lmtreser/Arduino-VGA-Games/case/images/buttoncap110.png

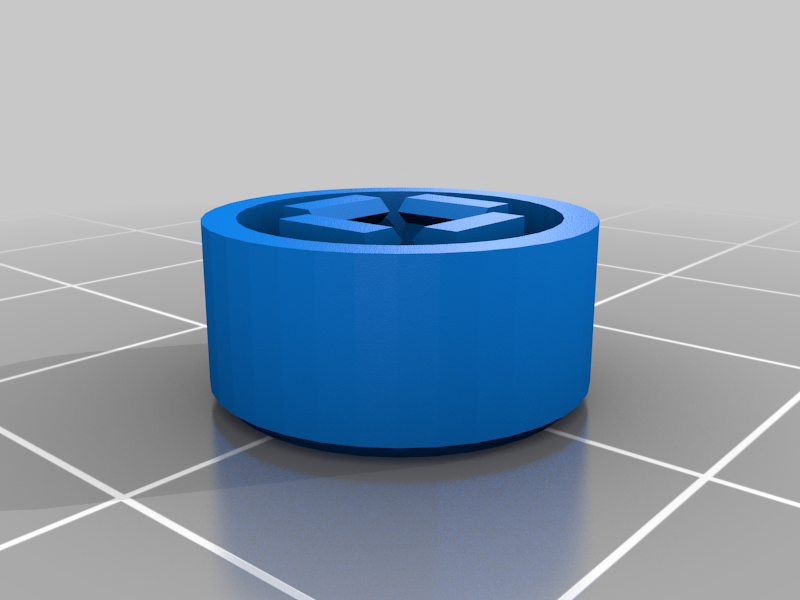
case/images/buttoncap110.png
