lmtreser/Arduino-VGA-Games/case/images/paddleknob.png

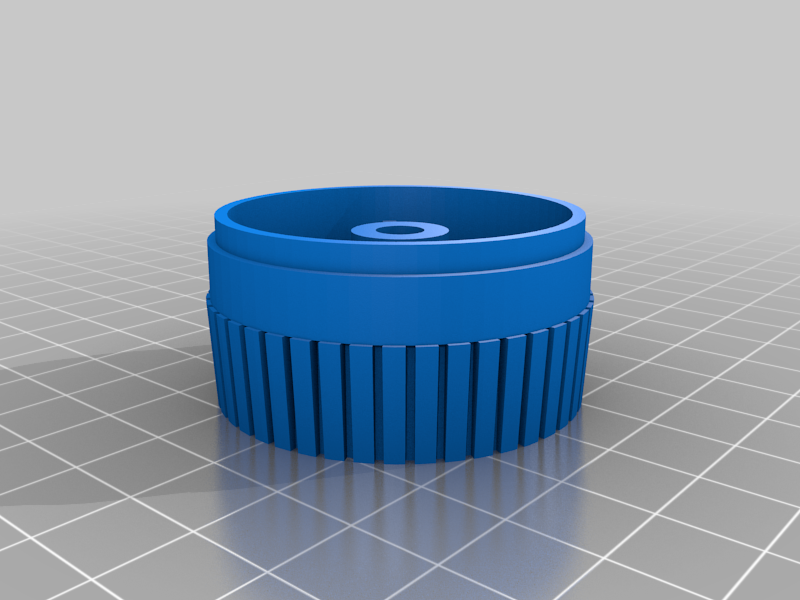
case/images/paddleknob.png
