lmtreser/Arduino-VGA-Games/case/images/paddlemain.png

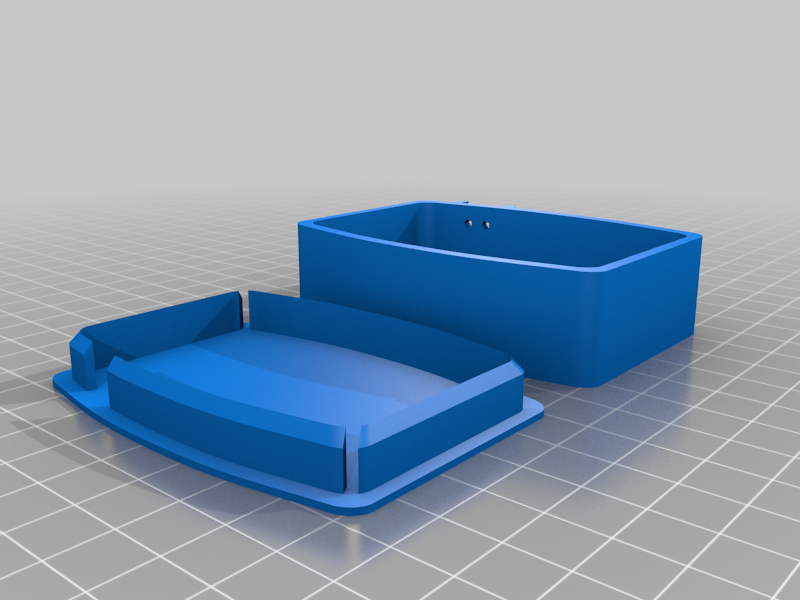
case/images/paddlemain.png
